Shivansh21git/Custom-ESP32/Screenshot (101).png

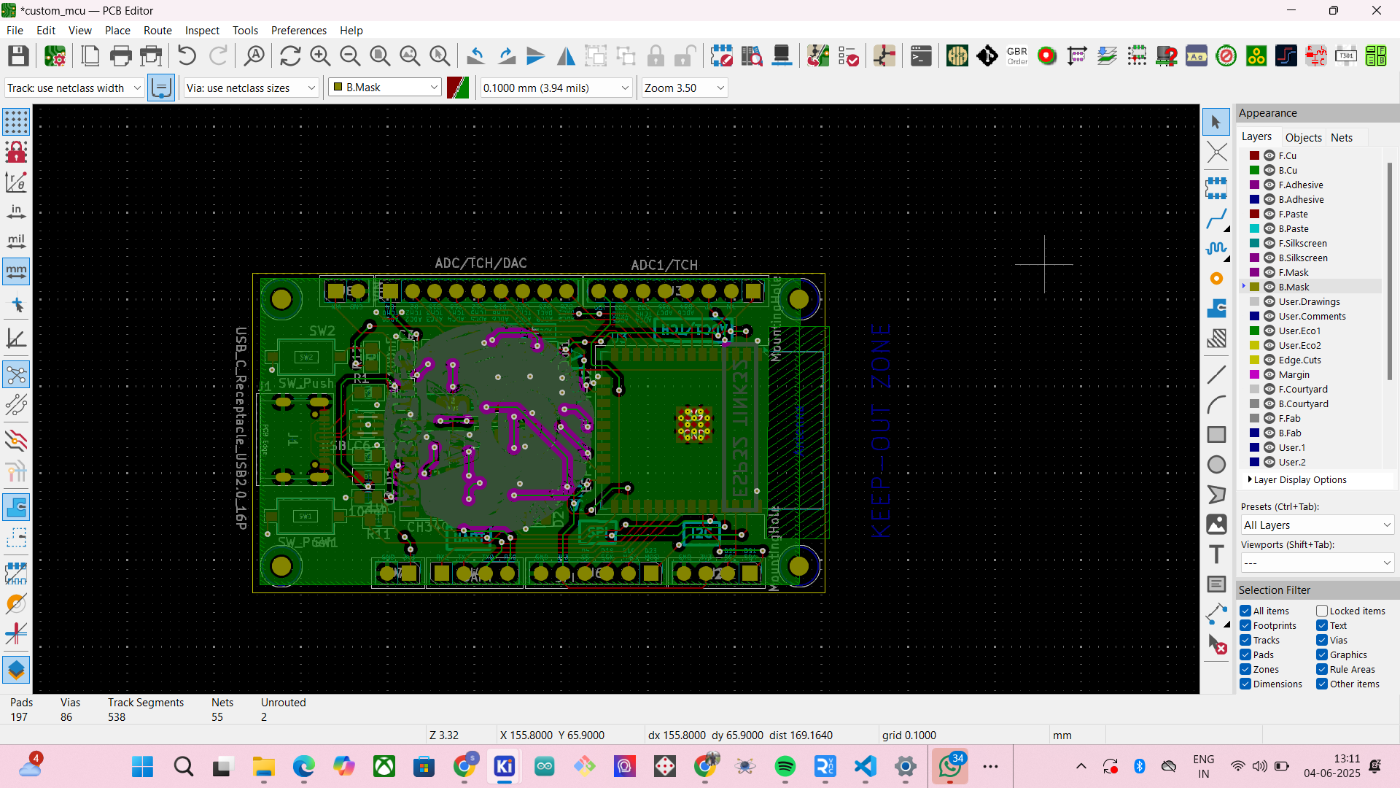
Screenshot (101).png
